case06/libresolarbox-v2_mobile/cadfiles/images/batterymount1c.png

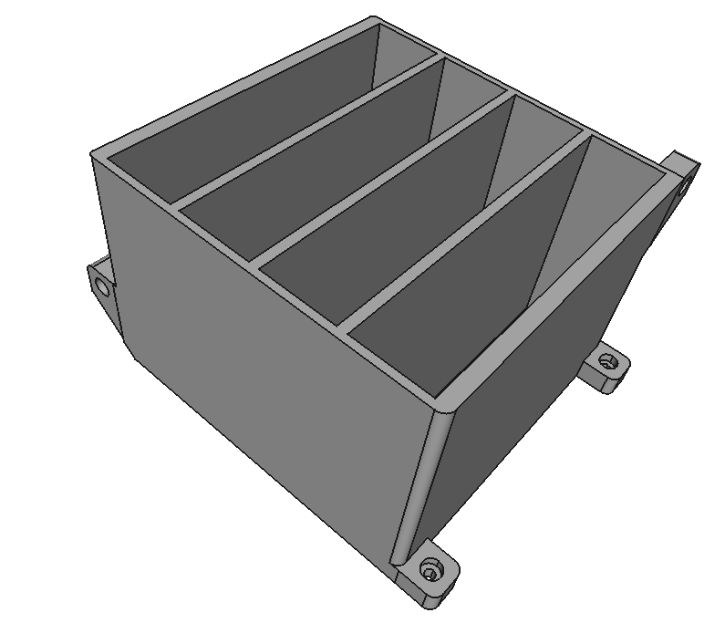
cadfiles/images/batterymount1c.png
