case06/libresolarbox-v2_mobile/cadfiles/images/batterymount_full-closure.PNG

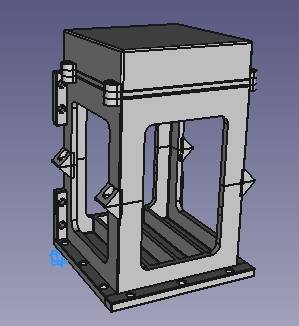
cadfiles/images/batterymount_full-closure.PNG
