case06/libresolarbox-v2_mobile/cadfiles/images/bms-case1h_box.png

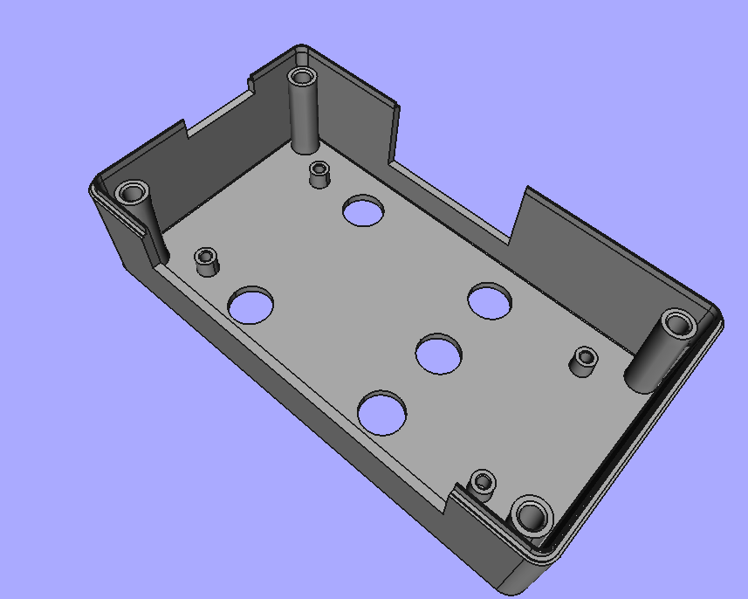
cadfiles/images/bms-case1h_box.png
