case06/libresolarbox-v2_mobile/cadfiles/images/bmscase1h_as.jpg

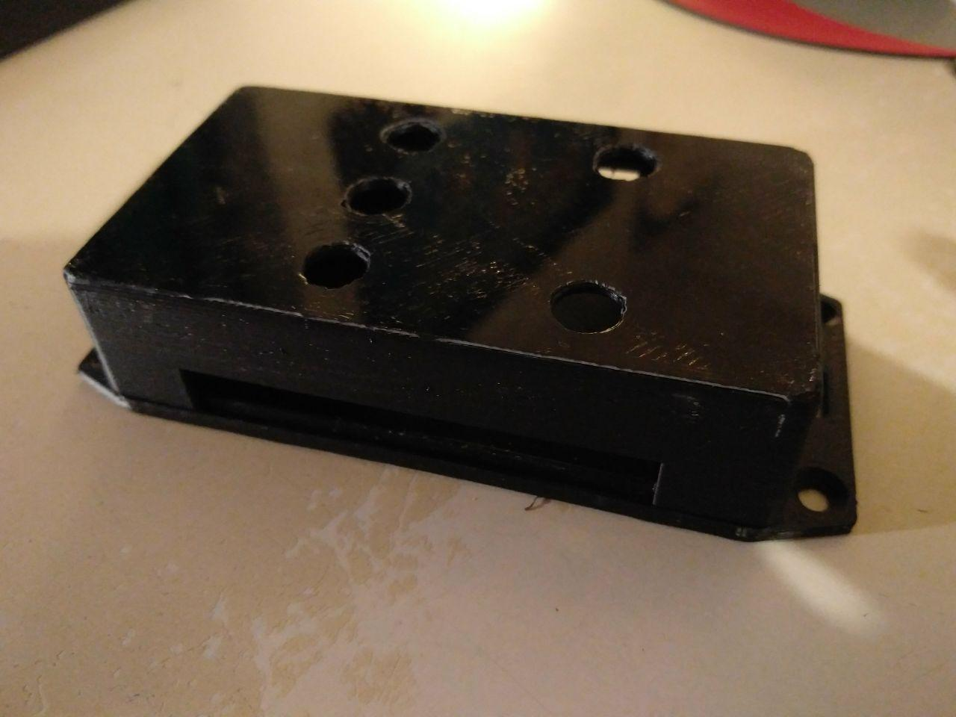
cadfiles/images/bmscase1h_as.jpg
