case06/libresolarbox-v2_mobile/cadfiles/images/bmscase1h_sp.jpg

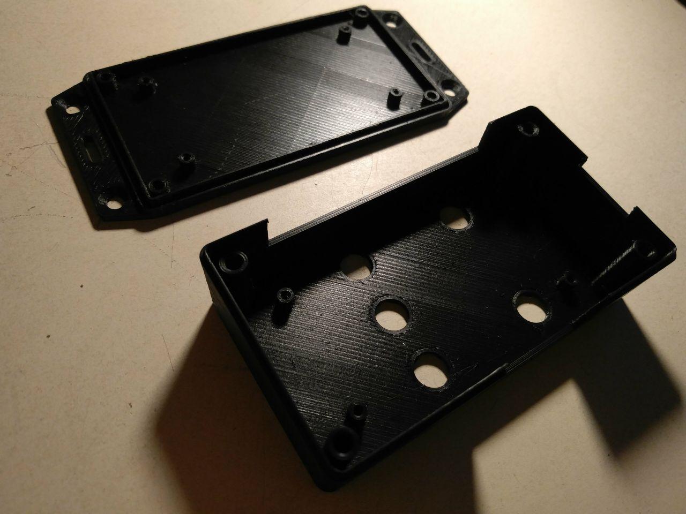
cadfiles/images/bmscase1h_sp.jpg
