case06/libresolarbox-v2_mobile/cadfiles/images/cam72_calb3.png

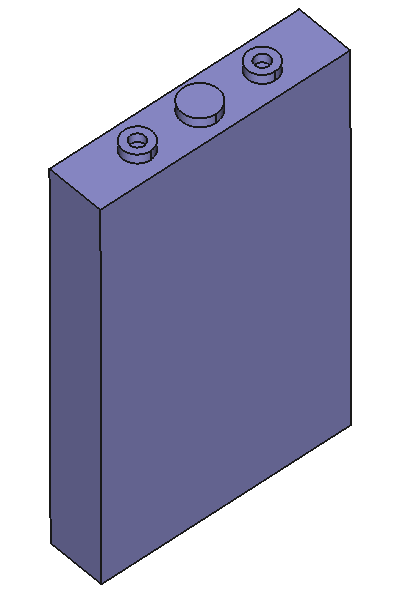
cadfiles/images/cam72_calb3.png
