case06/libresolarbox-v2_mobile/cadfiles/images/cam72_calb3_dimensions.png

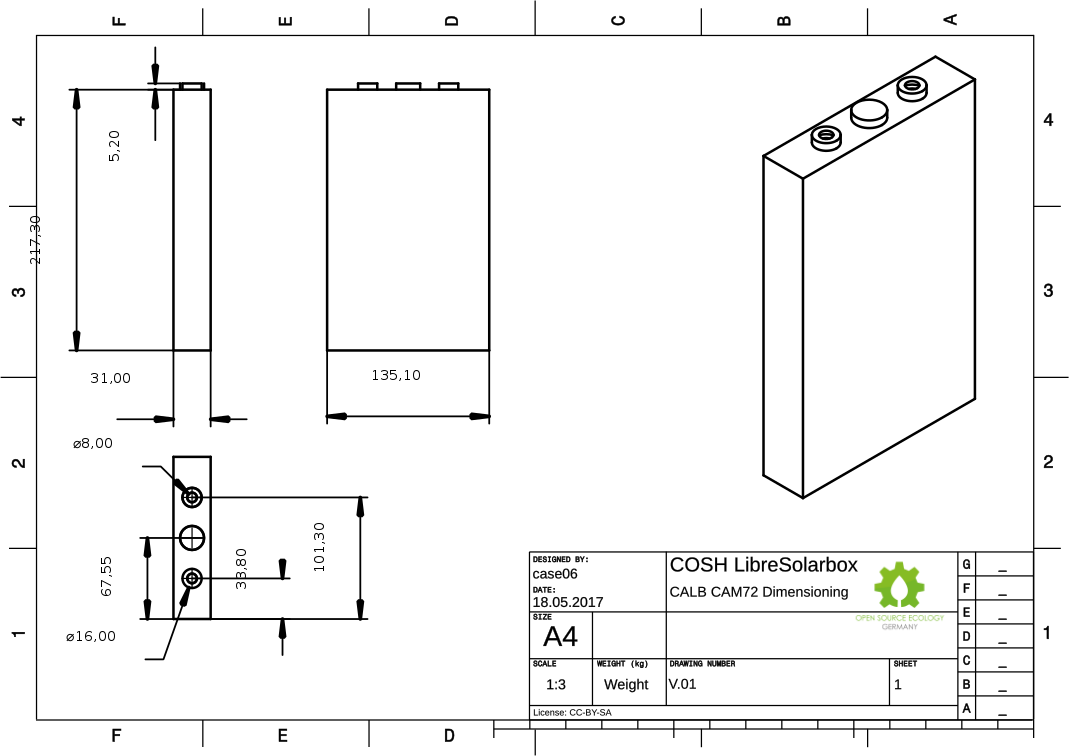
cadfiles/images/cam72_calb3_dimensions.png
