case06/libresolarbox-v2_mobile/cadfiles/images/front_dimensions.png

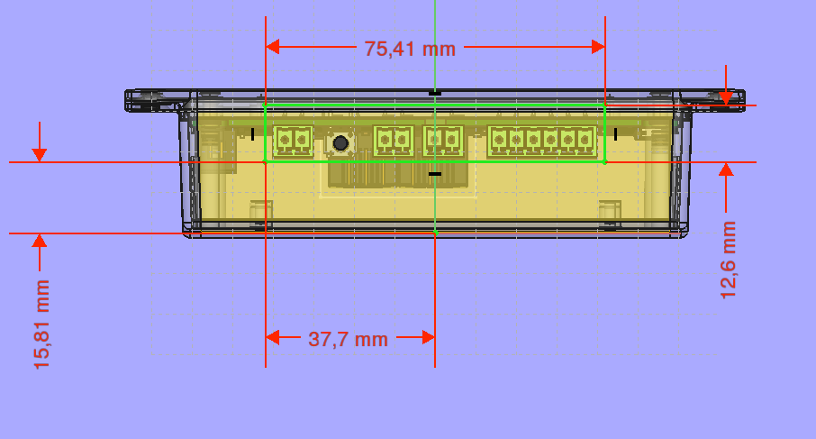
cadfiles/images/front_dimensions.png
