case06/libresolarbox-v2_mobile/cadfiles/images/Photo_2018-04-28_18-47-50.jpg

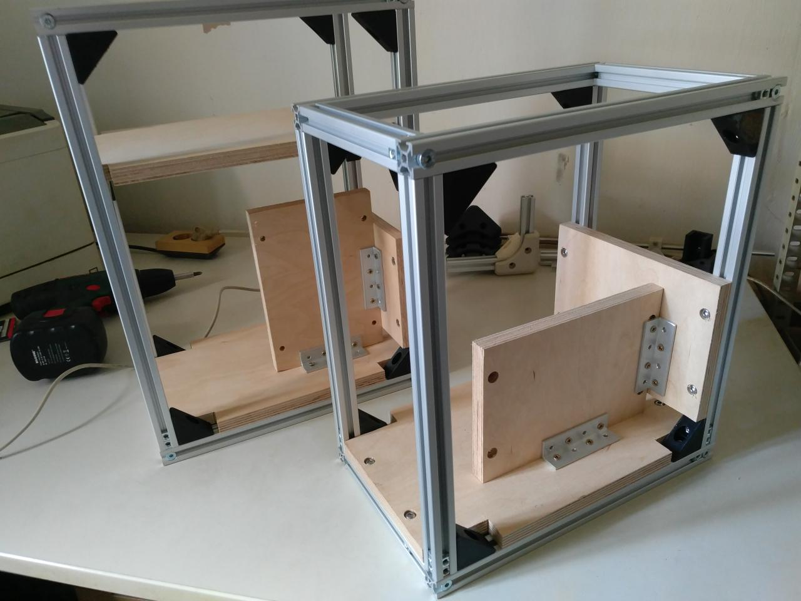
cadfiles/images/Photo_2018-04-28_18-47-50.jpg
