case06/libresolarbox-v2_mobile/cadfiles/images/Photo_2018-04-28_18-48-03.jpg

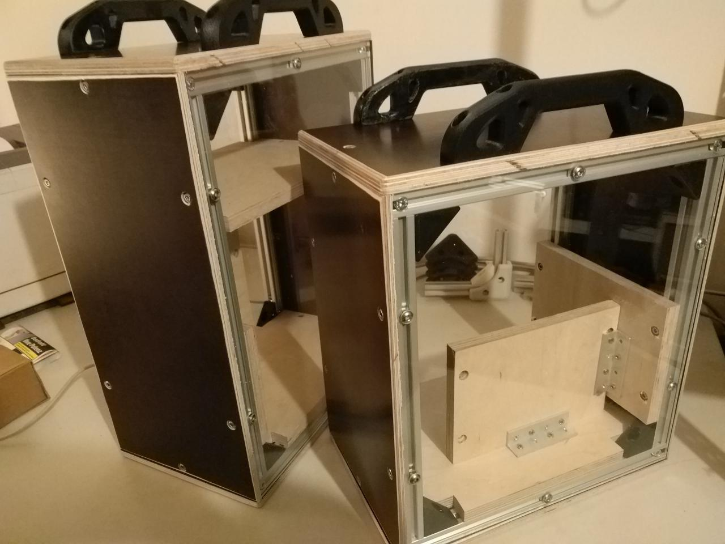
cadfiles/images/Photo_2018-04-28_18-48-03.jpg
