case06/libresolarbox-v2_mobile/cadfiles/images/sideCoverNG2.png

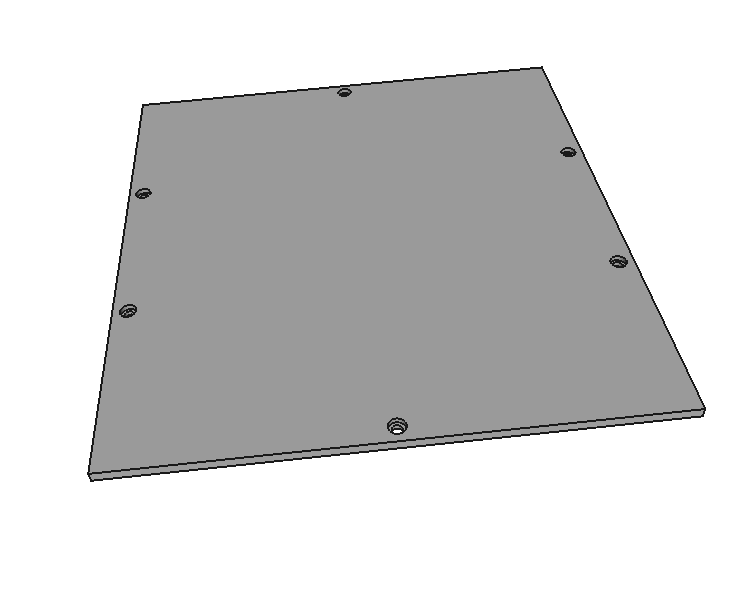
cadfiles/images/sideCoverNG2.png
