case06/libresolarbox-v2_mobile/cadfiles/images/sideCoverNG2_dim.png

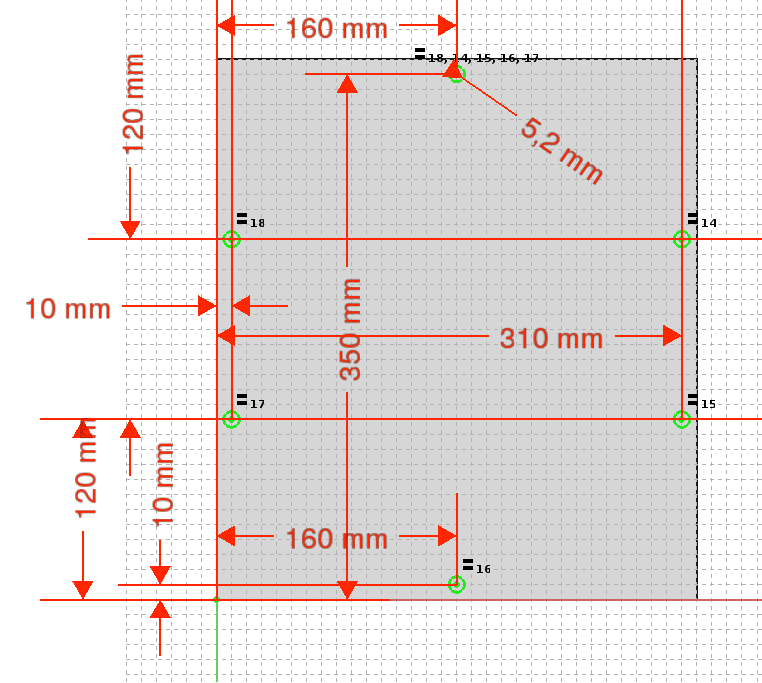
cadfiles/images/sideCoverNG2_dim.png
