case06/libresolarbox-v2_mobile/cadfiles/images/top_dimensions.png

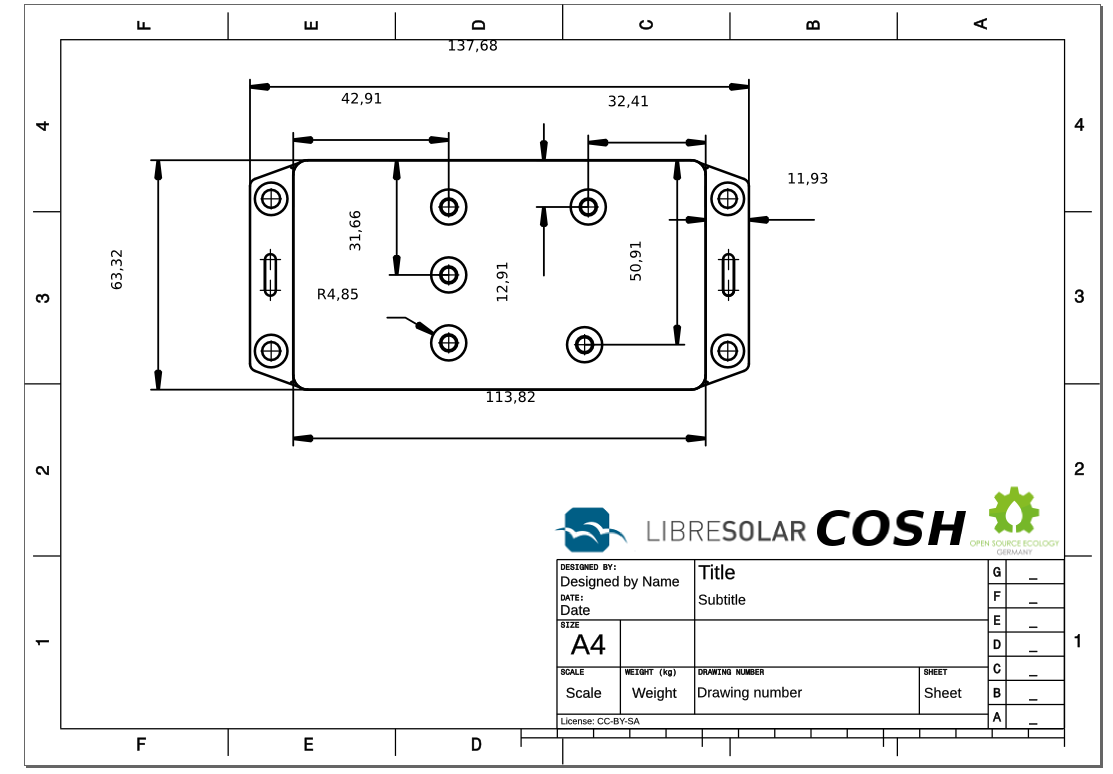
cadfiles/images/top_dimensions.png
