case06/libresolarbox-v2_mobile/cadfiles/images/topbottomNG2_dim.png

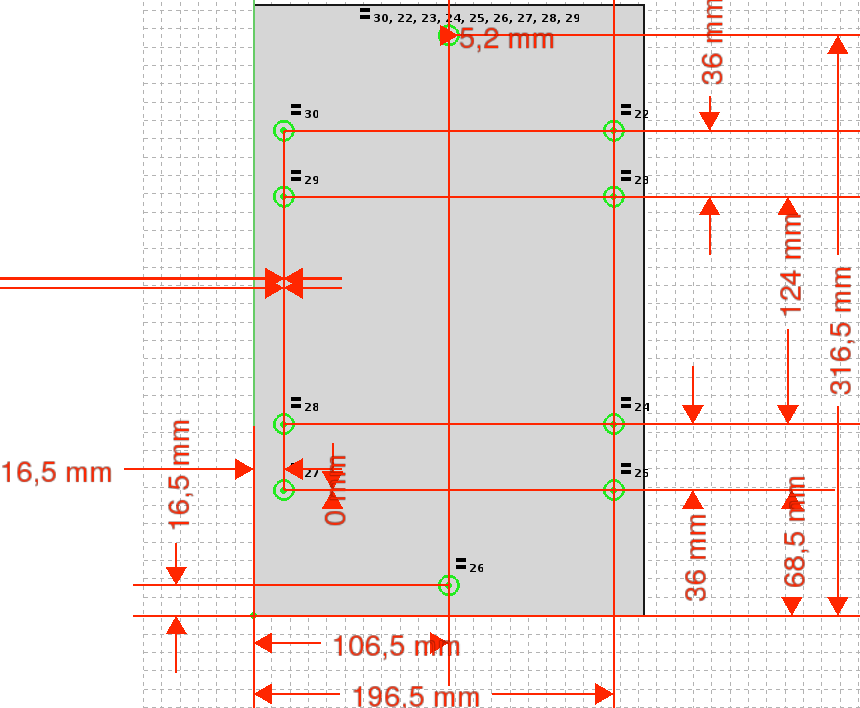
cadfiles/images/topbottomNG2_dim.png
