case06/libresolarbox-v2_mobile/cadfiles/images/topbottomNG2b.png

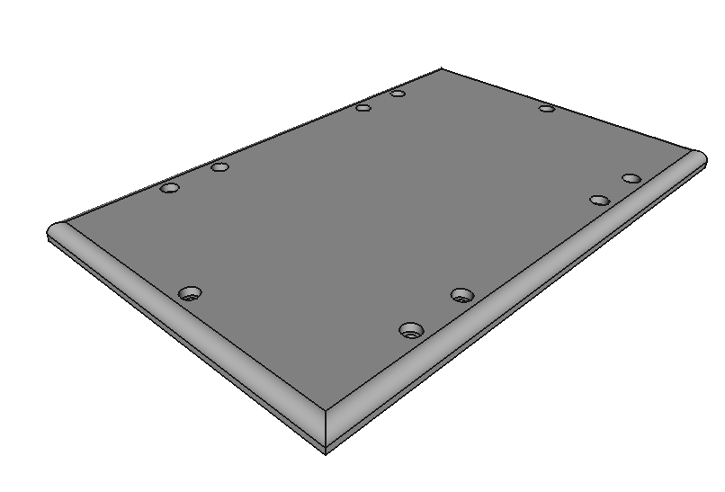
cadfiles/images/topbottomNG2b.png
