case06/libresolarbox-v2_mobile/cadfiles/images/UPKframeNG2b.png

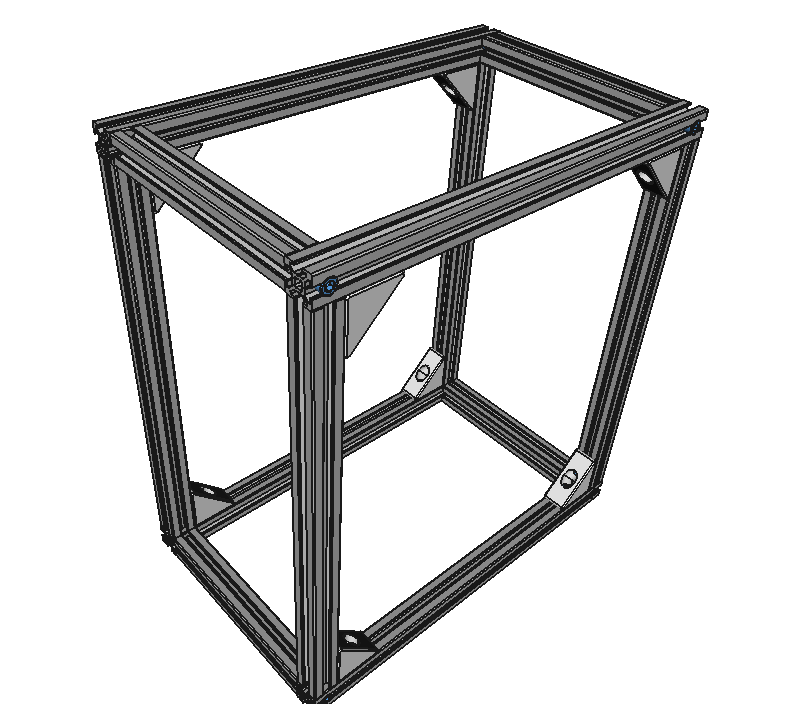
cadfiles/images/UPKframeNG2b.png
