case06/libresolarbox-v2_mobile/cadfiles/images/UPKframeNG2d.png

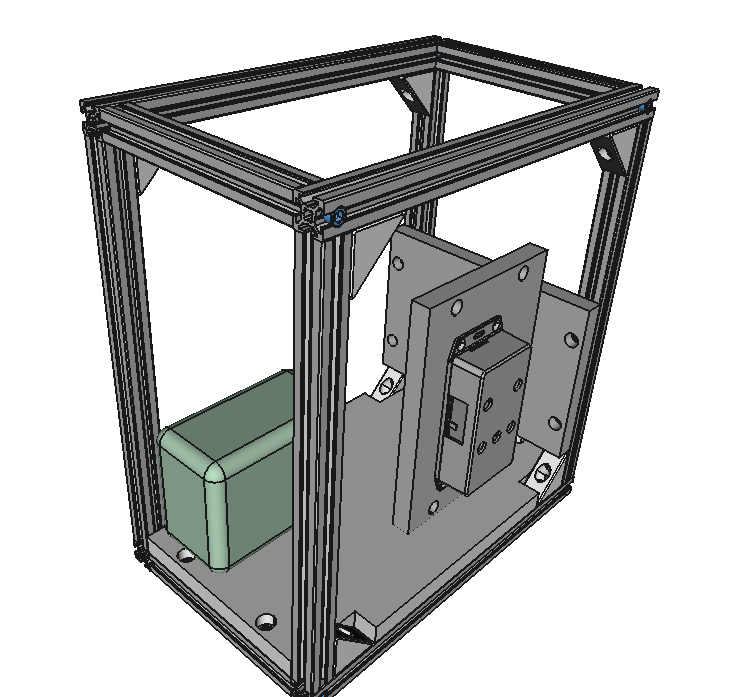
cadfiles/images/UPKframeNG2d.png
