case06/libresolarbox-v2_mobile/cadfiles/images/UPKframeNG2e.png

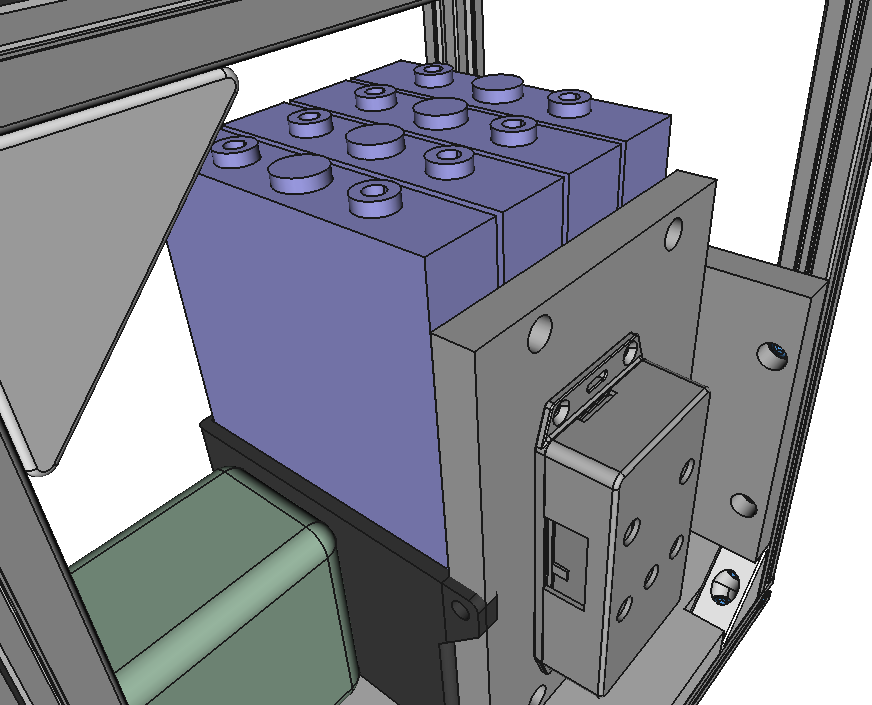
cadfiles/images/UPKframeNG2e.png
