case06/libresolarbox-v2_mobile/cadfiles/images/UPKframeNG2e_closeup.png

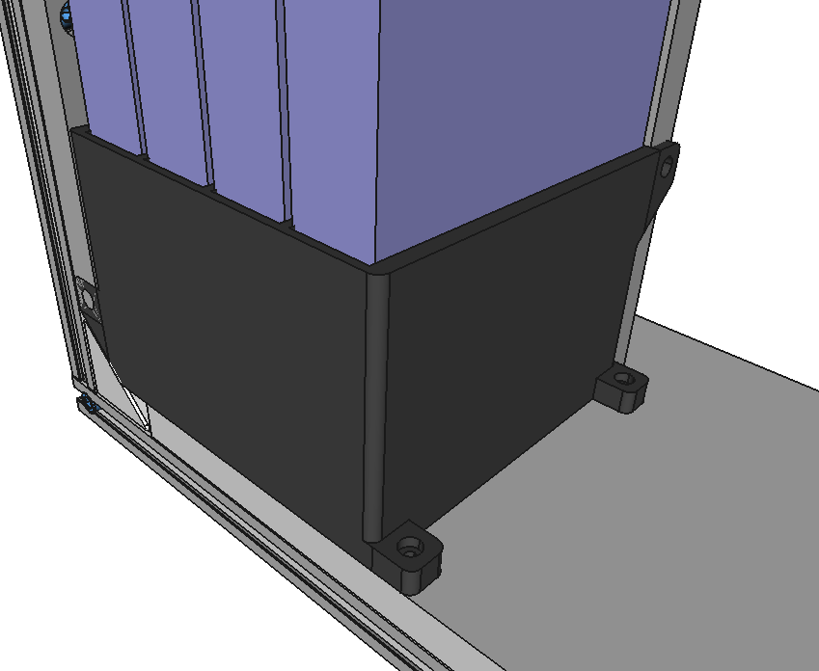
cadfiles/images/UPKframeNG2e_closeup.png
