case06/libresolarbox-v2_mobile/cadfiles/images/UPKframeNG2h_closeup.png

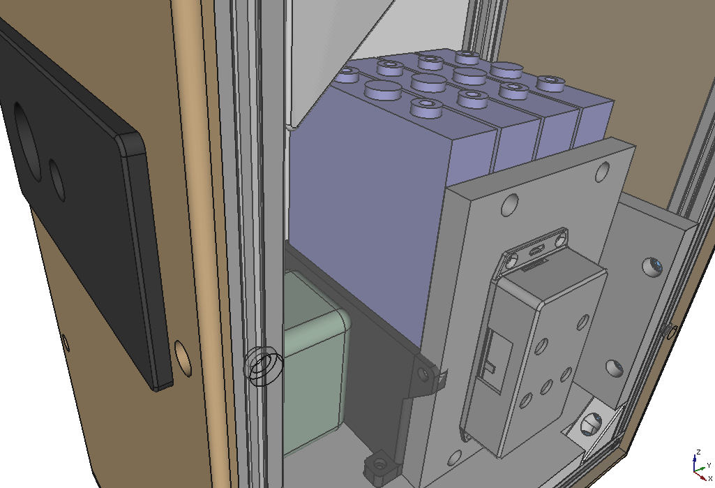
cadfiles/images/UPKframeNG2h_closeup.png
