case06/libresolarbox-v2_mobile/cadfiles/images/UPKframeNG2j.png

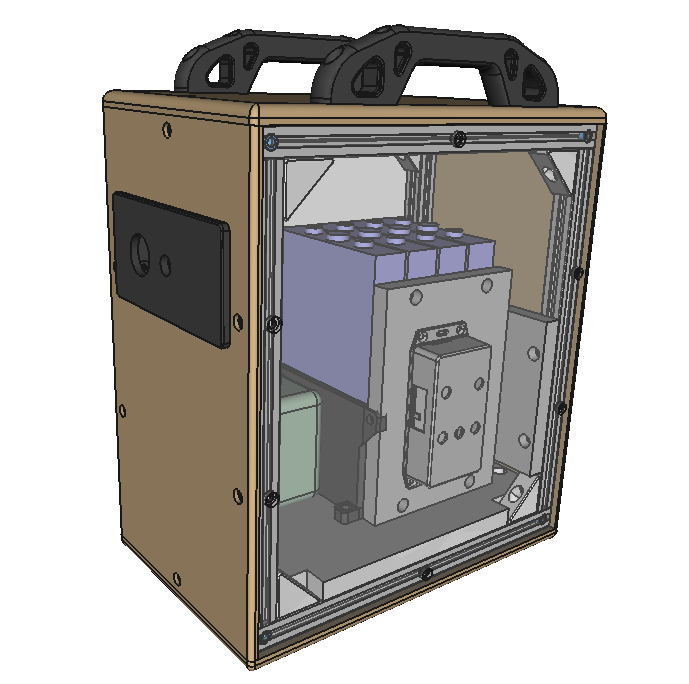
cadfiles/images/UPKframeNG2j.png
