case06/libresolarbox-v2_mobile/cadfiles/images/UPKframeNG2j_back.png

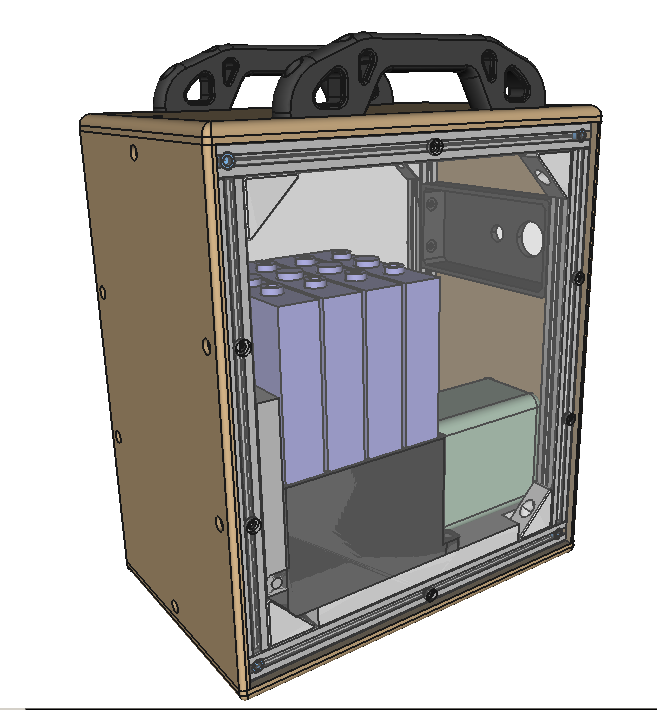
cadfiles/images/UPKframeNG2j_back.png
