case06/libresolarbox-v2_mobile/electronics/images/P7080123.JPG

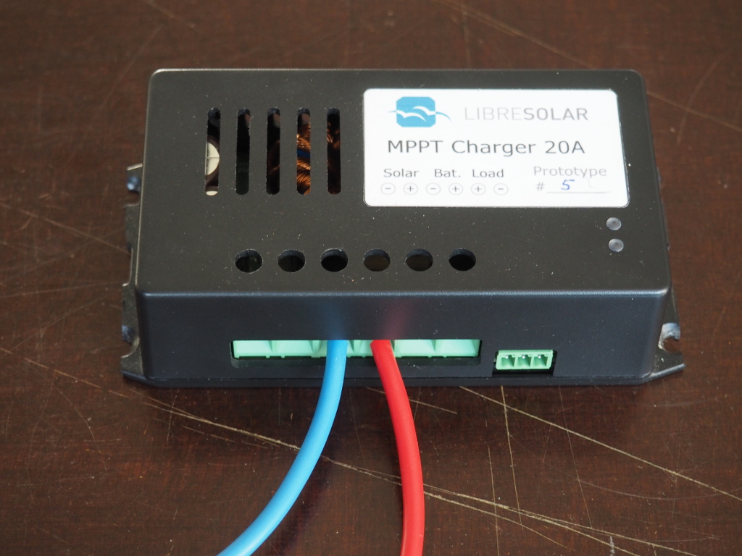
electronics/images/P7080123.JPG
