case06/libresolarbox-v2_mobile/cadfiles/cam72_calb3.fcstd

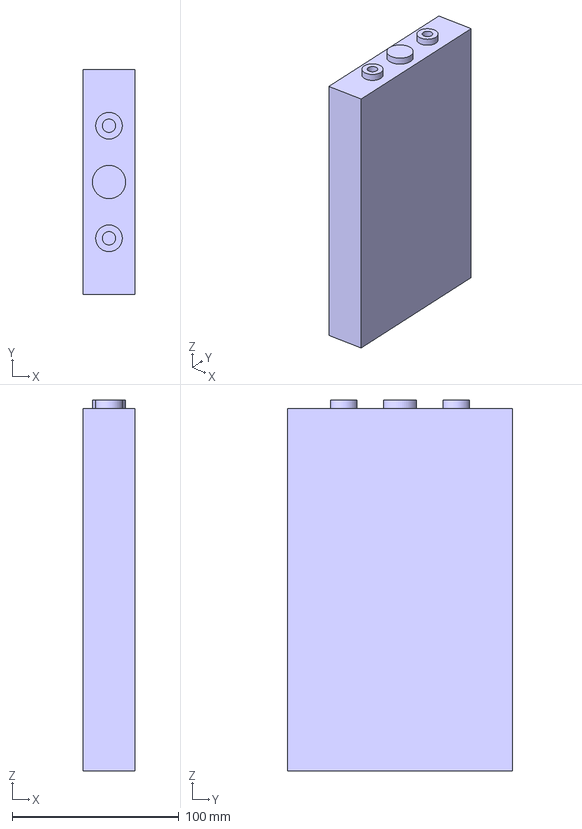
[picture p52: CAD file, 2021-08-01]
cadfiles/cam72_calb3.fcstd
31.0 x 135.1 x 222.5 mm
