case06/libresolarbox-v2_mobile/doc/src/src_boxassemblyguide1d/upright/upright5_all.fcstd

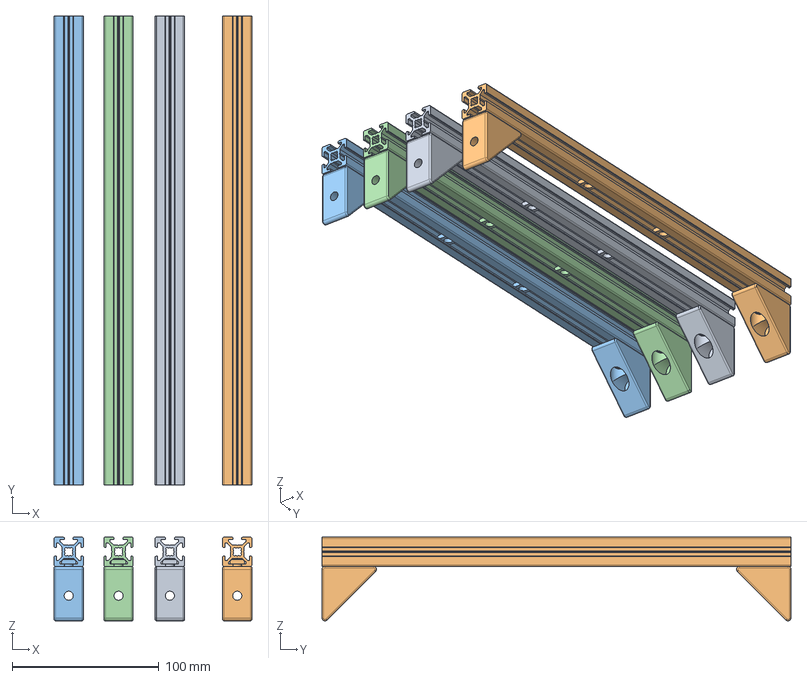
[picture p55: CAD file, 2021-08-01]
doc/src/src_boxassemblyguide1d/upright/upright5_all.fcstd
135.0 x 320.0 x 57.2 mm
