case06/libresolarbox-v2_mobile/doc/src/src_boxassemblyguide1d/upright/upright3_ex.fcstd

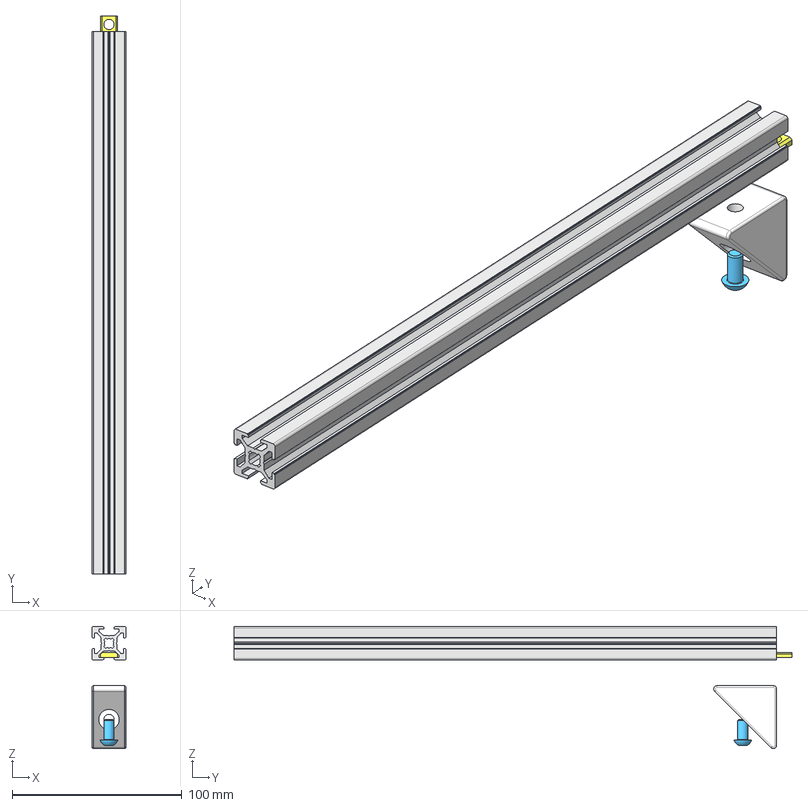
[picture p58: CAD file, 2021-08-01]
doc/src/src_boxassemblyguide1d/upright/upright3_ex.fcstd
20.0 x 329.0 x 72.2 mm
tslot32
m6nutplate
M6x12-Screw001
RAcorner
