case06/libresolarbox-v2_mobile/doc/src/src_boxassemblyguide1d/rawframe/rawframe2.fcstd

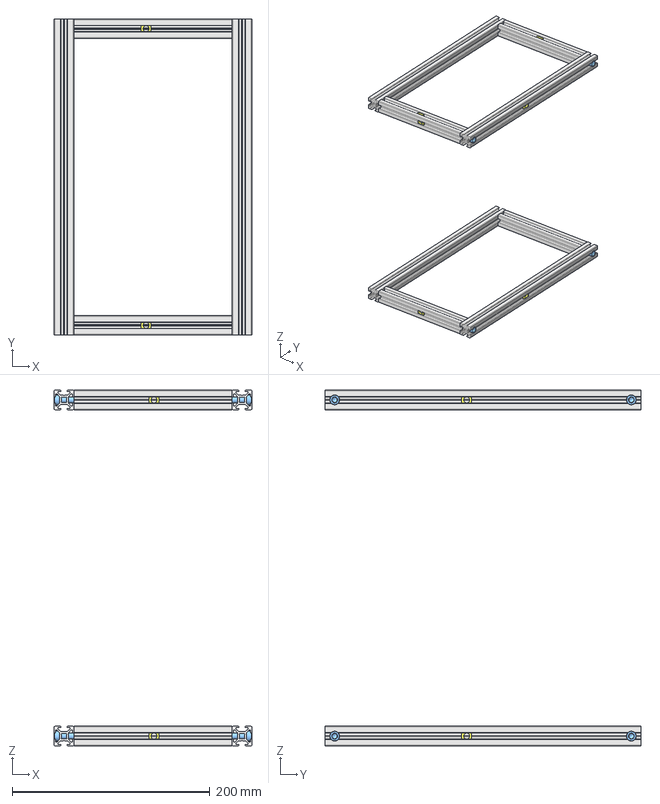
[picture p59: CAD file, 2021-08-01]
doc/src/src_boxassemblyguide1d/rawframe/rawframe2.fcstd
200.0 x 320.0 x 360.0 mm
tslot32con
tslot16
tslot16_001
tslot32con_001
M6x25-Screw
M6x25-Screw004
M6x25-Screw005
M6x25-Screw006
tslot32con001
tslot041
tslot16_002
tslot32con_002
M6x25-Screw012
M6x25-Screw015
M6x25-Screw017
M6x25-Screw016
m6nutplate020uf
m6nutplate021lf
m6nutplate022lf
m6nutplate023lf
m6nutplate024lf
m6nutplate025lf
m6nutplate026lf
m6nutplate027lf
m6nutplate028uf
m6nutplate029uf
m6nutplate030lf
m6nutplate031lf
m6nutplate032uf
m6nutplate033lf
m6nutplate025uf001
m6nutplate022uf001
