case06/libresolarbox-v2_mobile/doc/src/src_boxassemblyguide1d/upright/upright3.fcstd

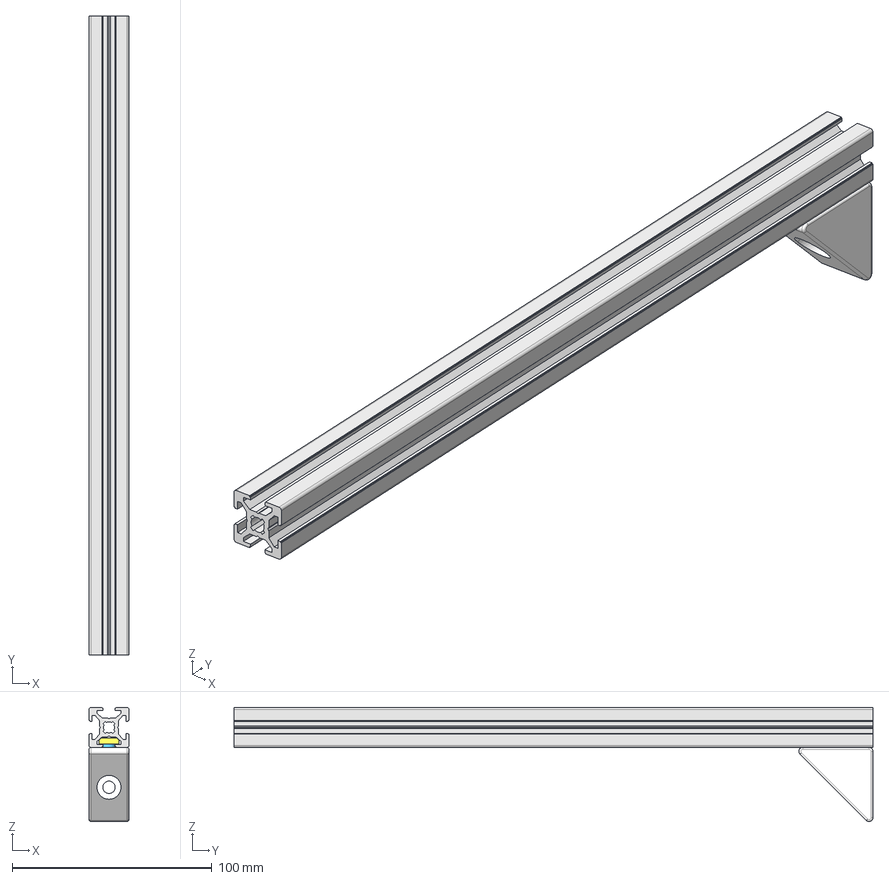
[picture p60: CAD file, 2021-08-01]
doc/src/src_boxassemblyguide1d/upright/upright3.fcstd
20.0 x 320.0 x 57.2 mm
tslot32
m6nutplate
M6x12-Screw001
RAcorner
