case06/libresolarbox-v2_mobile/doc/src/src_boxassemblyguide1d/upright/upright1.fcstd

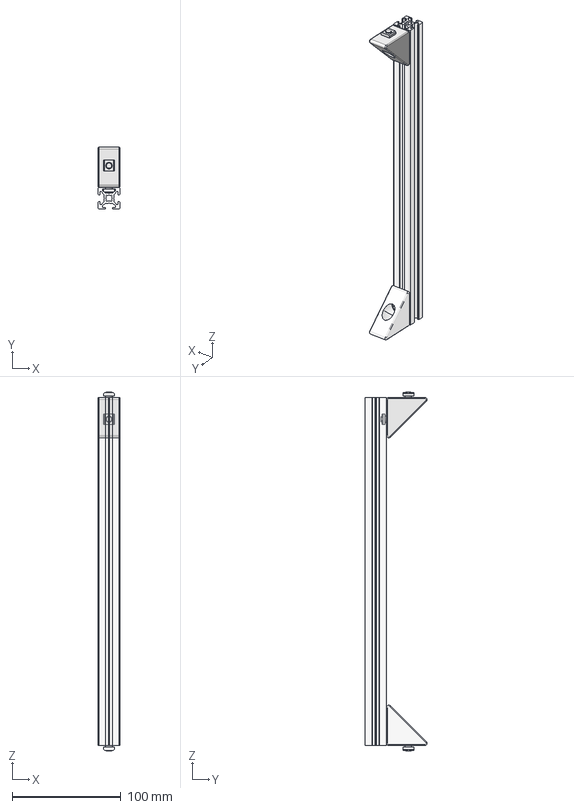
[picture p61: CAD file, 2021-08-01]
doc/src/src_boxassemblyguide1d/upright/upright1.fcstd
20.0 x 57.2 x 330.0 mm
tslot32_001
