case06/libresolarbox-v2_mobile/doc/src/images/assembly_day_08.07.18/P7080107.JPG

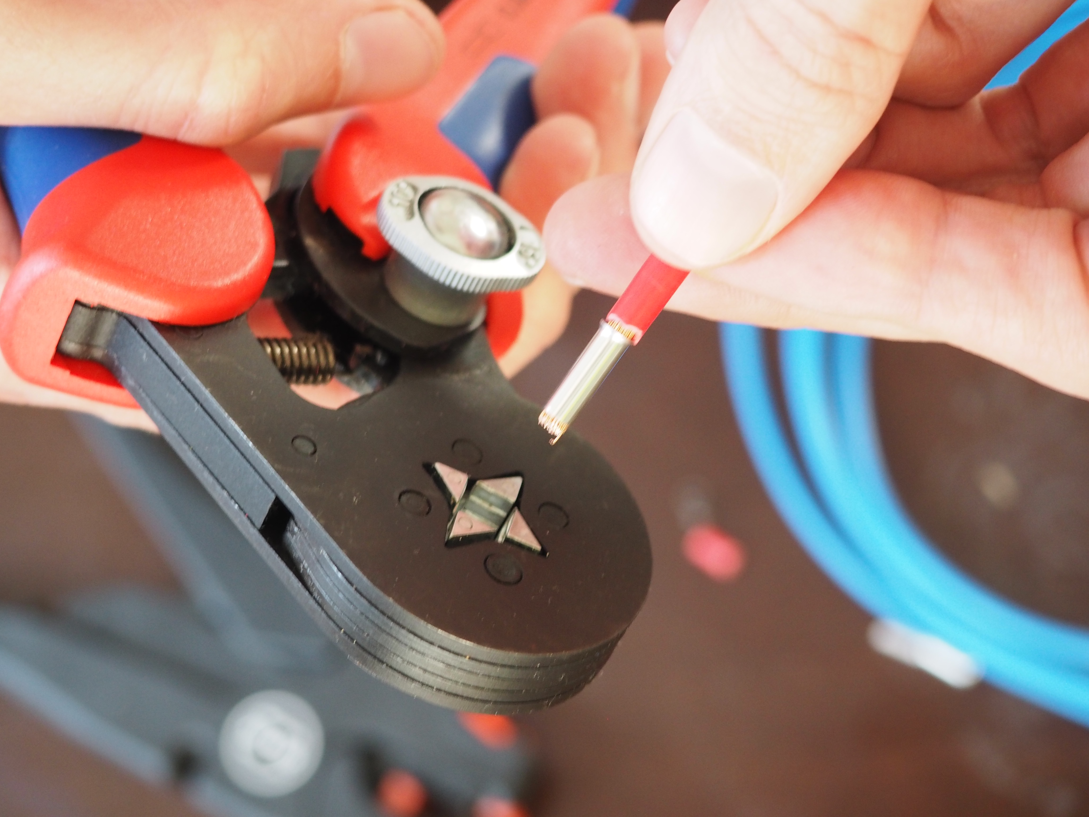
doc/src/images/assembly_day_08.07.18/P7080107.JPG
