case06/libresolarbox-v2_mobile/doc/src/src_boxassemblyguide1d/box-assemblyguide/images/titlepage.png

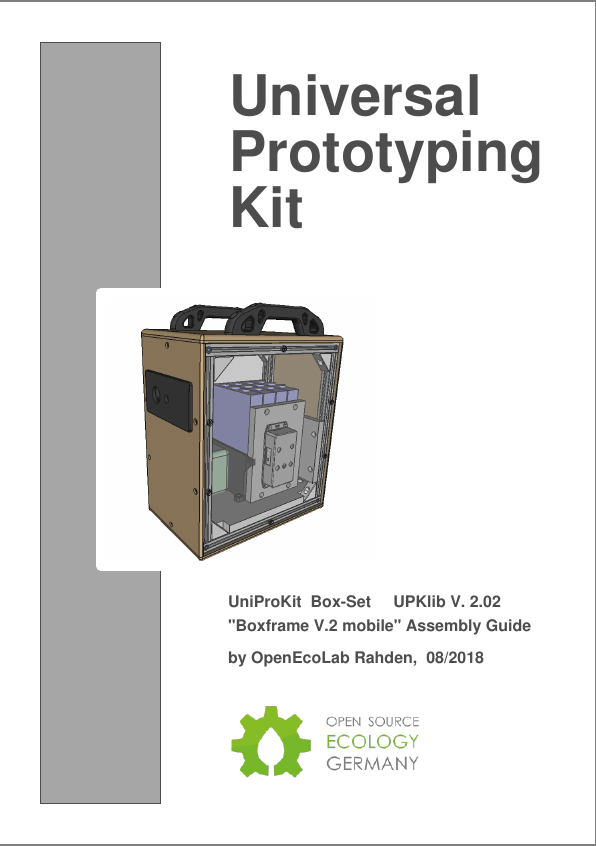
doc/src/src_boxassemblyguide1d/box-assemblyguide/images/titlepage.png
