case06/libresolarbox-v2_mobile/doc/src/src_boxassemblyguide1d/cover/cov10.png

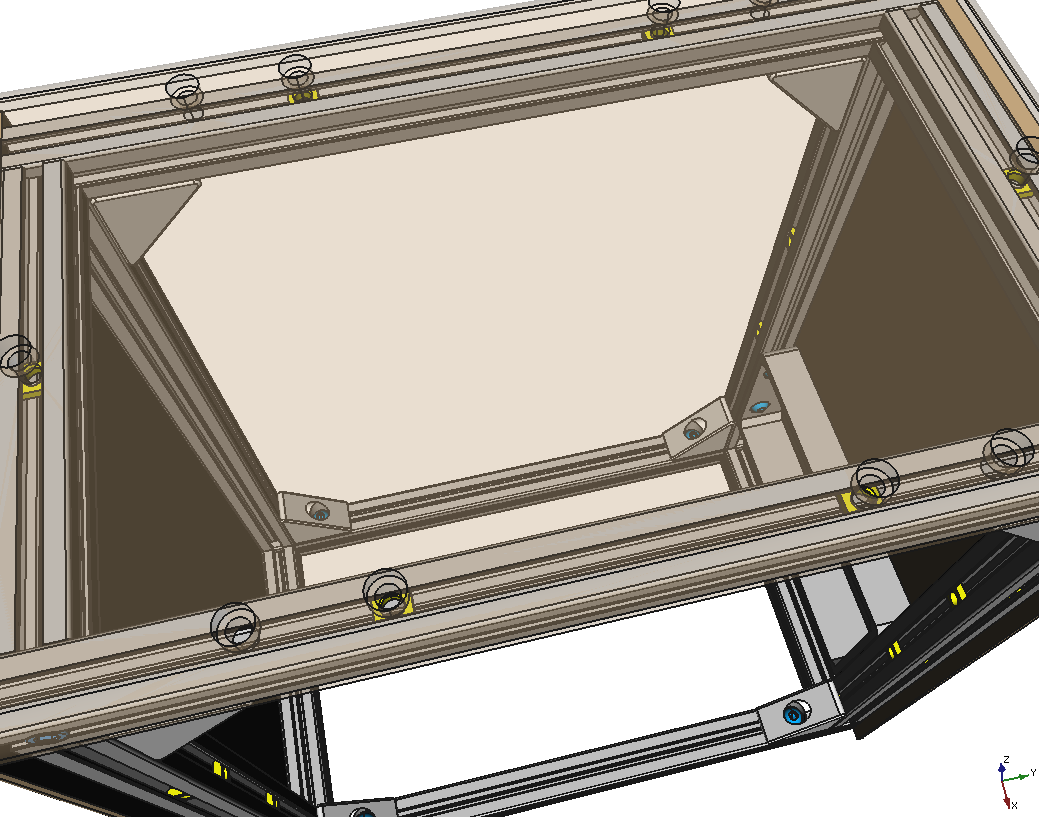
doc/src/src_boxassemblyguide1d/cover/cov10.png
