case06/libresolarbox-v2_mobile/doc/src/src_boxassemblyguide1d/cover/cov16.png

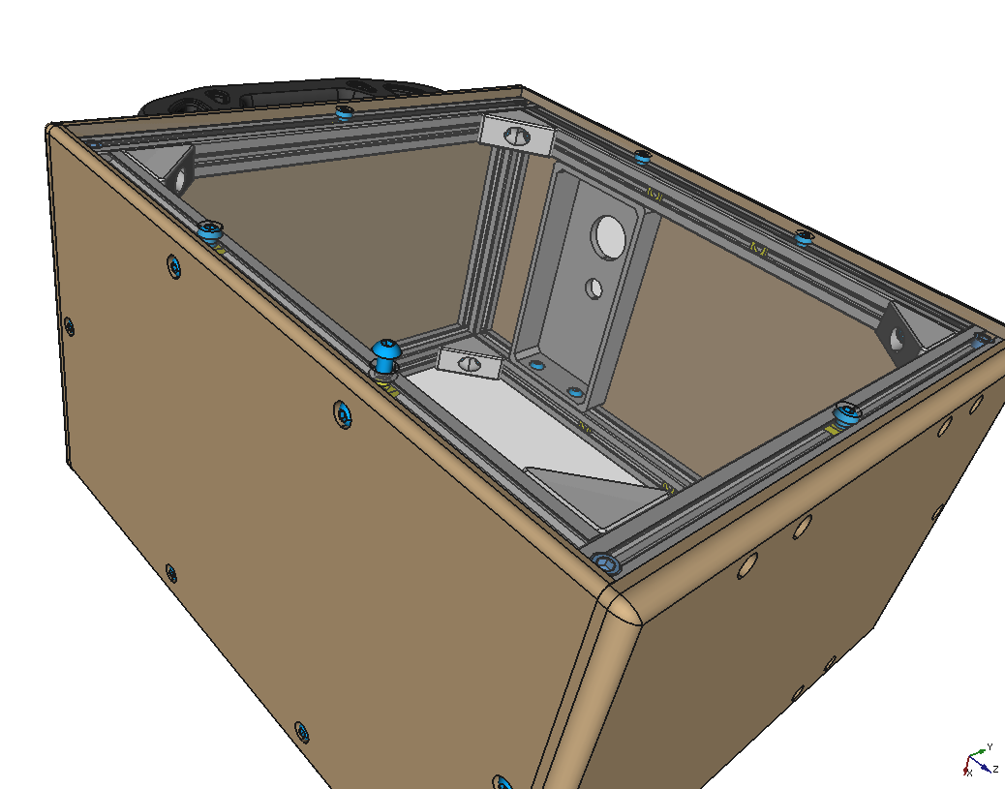
doc/src/src_boxassemblyguide1d/cover/cov16.png
