case06/libresolarbox-v2_mobile/doc/src/src_boxassemblyguide1d/ifmountframe/ifmount1.png

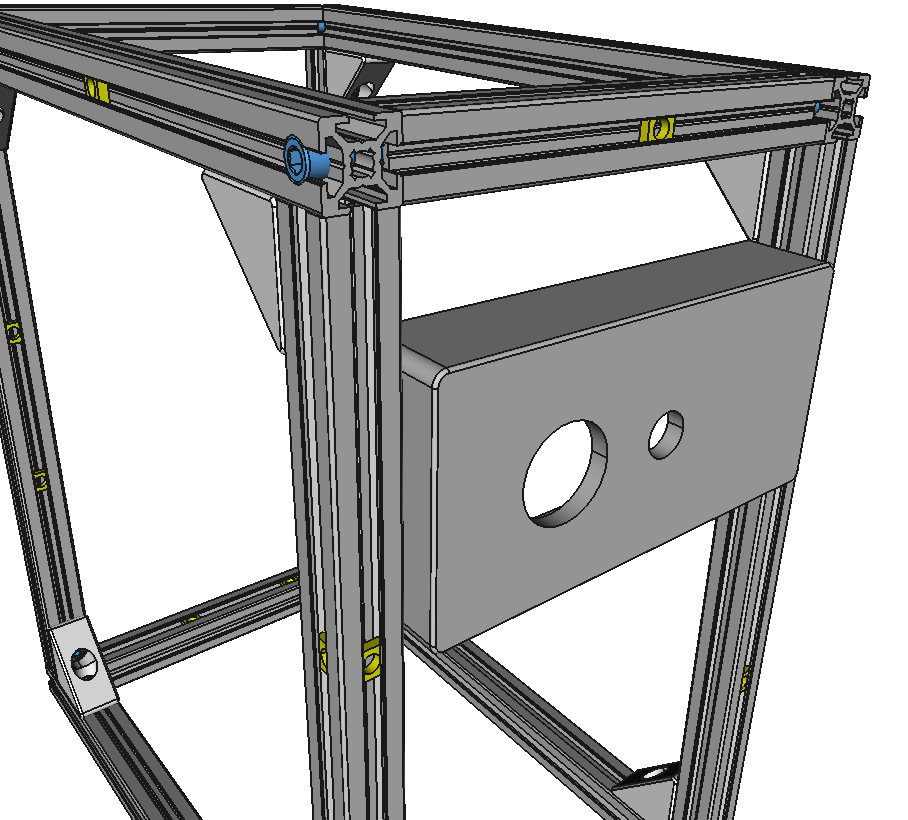
doc/src/src_boxassemblyguide1d/ifmountframe/ifmount1.png
