case06/libresolarbox-v2_mobile/doc/src/src_boxassemblyguide1d/innerplates/bottom1b.png

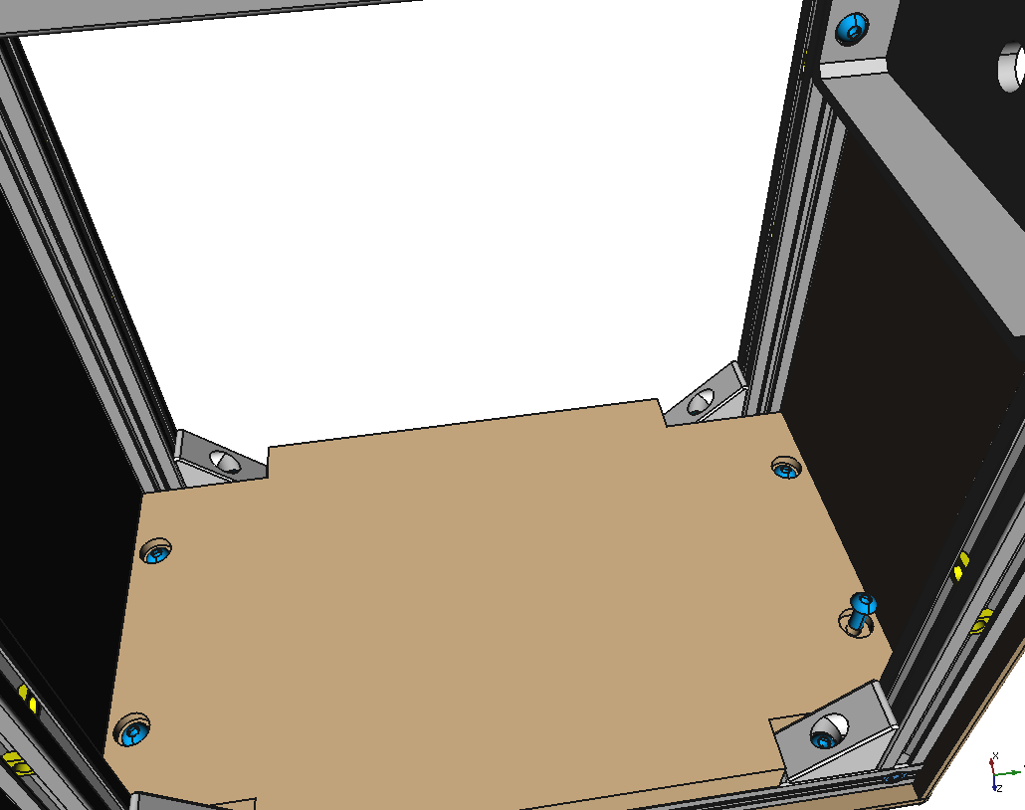
doc/src/src_boxassemblyguide1d/innerplates/bottom1b.png
