case06/libresolarbox-v2_mobile/doc/src/src_boxassemblyguide1d/innerplates/front4c.png

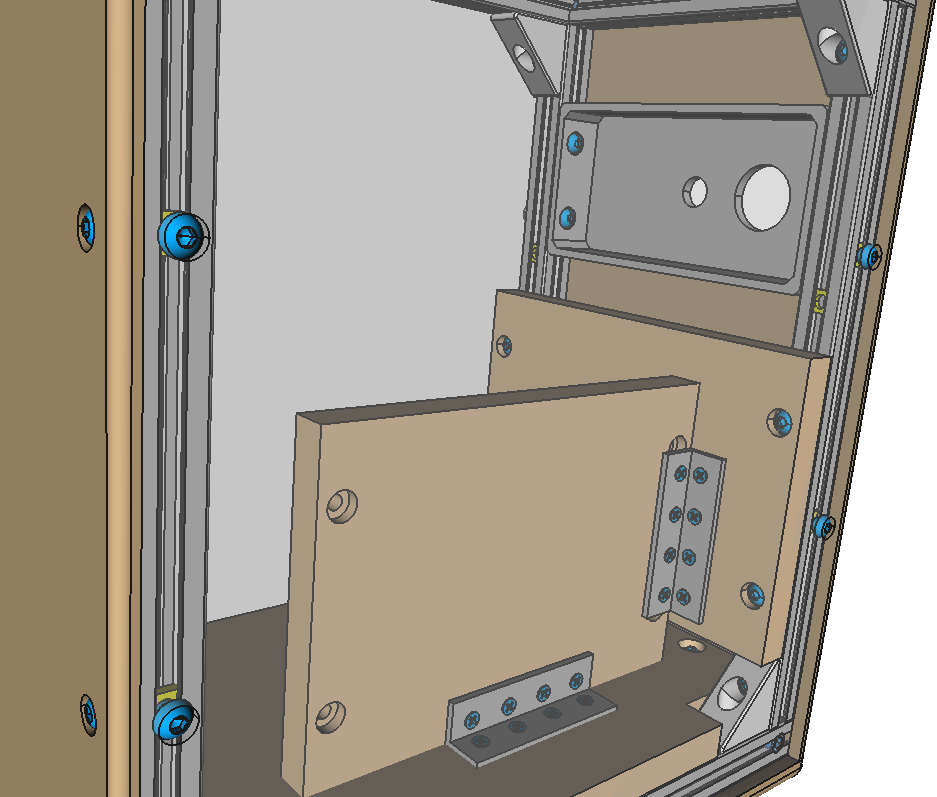
doc/src/src_boxassemblyguide1d/innerplates/front4c.png
