case06/libresolarbox-v2_mobile/doc/src/src_boxassemblyguide1d/lower_frame/lframe2.png

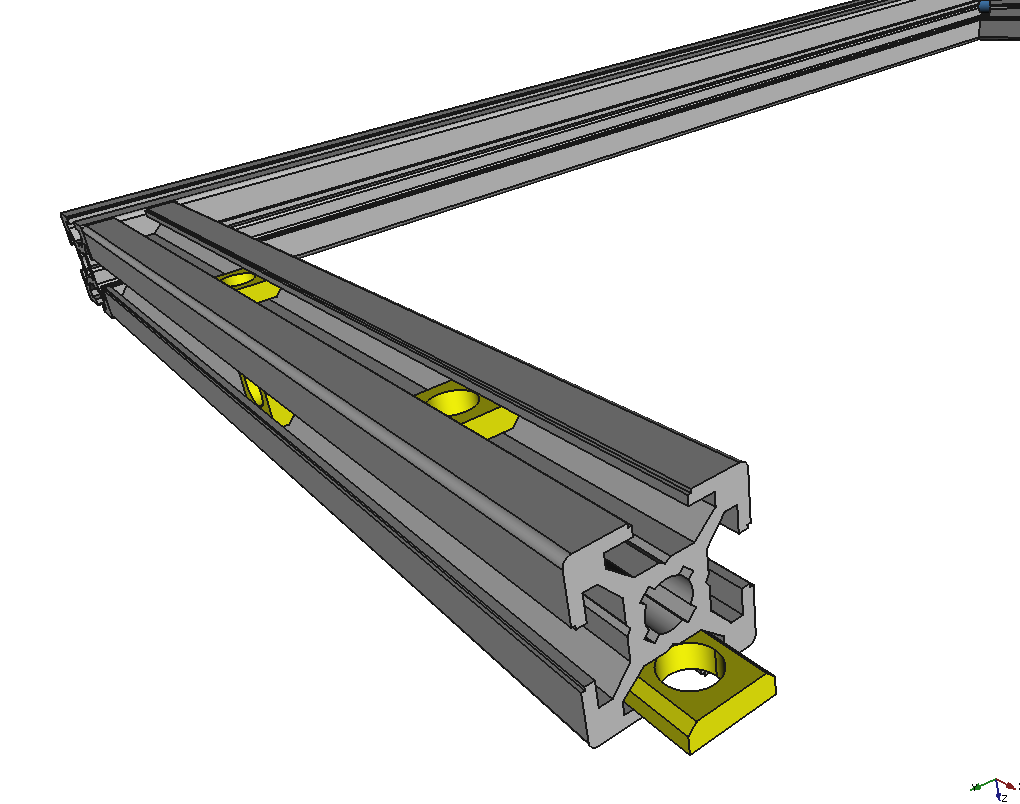
doc/src/src_boxassemblyguide1d/lower_frame/lframe2.png
