case06/libresolarbox-v2_mobile/doc/src/src_boxassemblyguide1d/lower_frame/lframe3.png

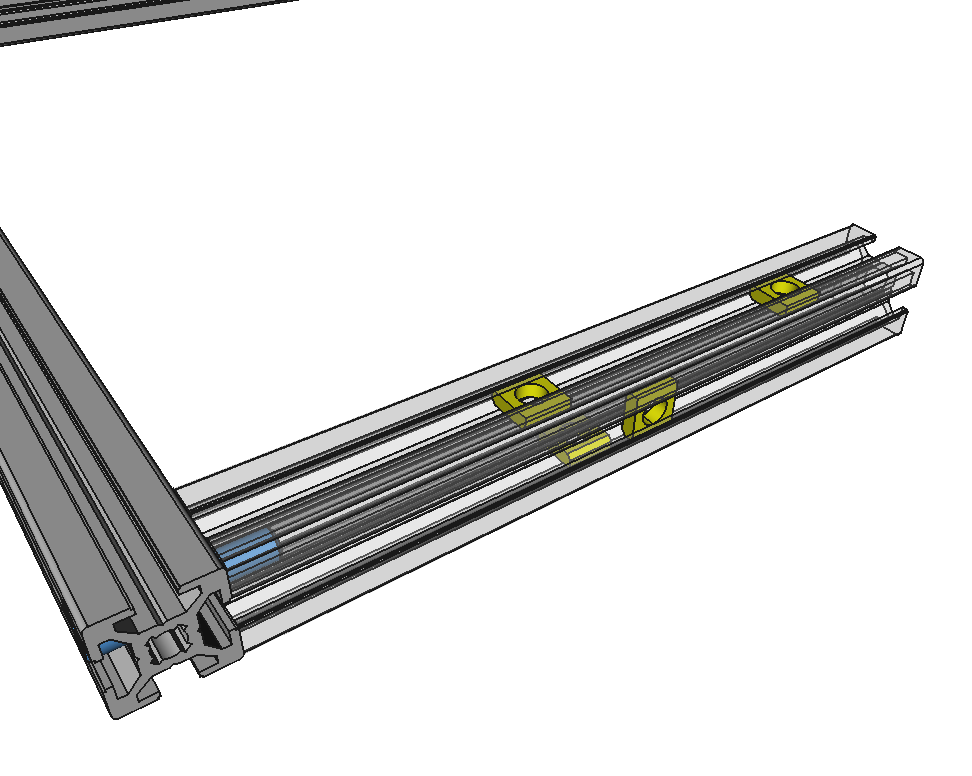
doc/src/src_boxassemblyguide1d/lower_frame/lframe3.png
