case06/libresolarbox-v2_mobile/doc/src/src_boxassemblyguide1d/rawframe/junction2.png

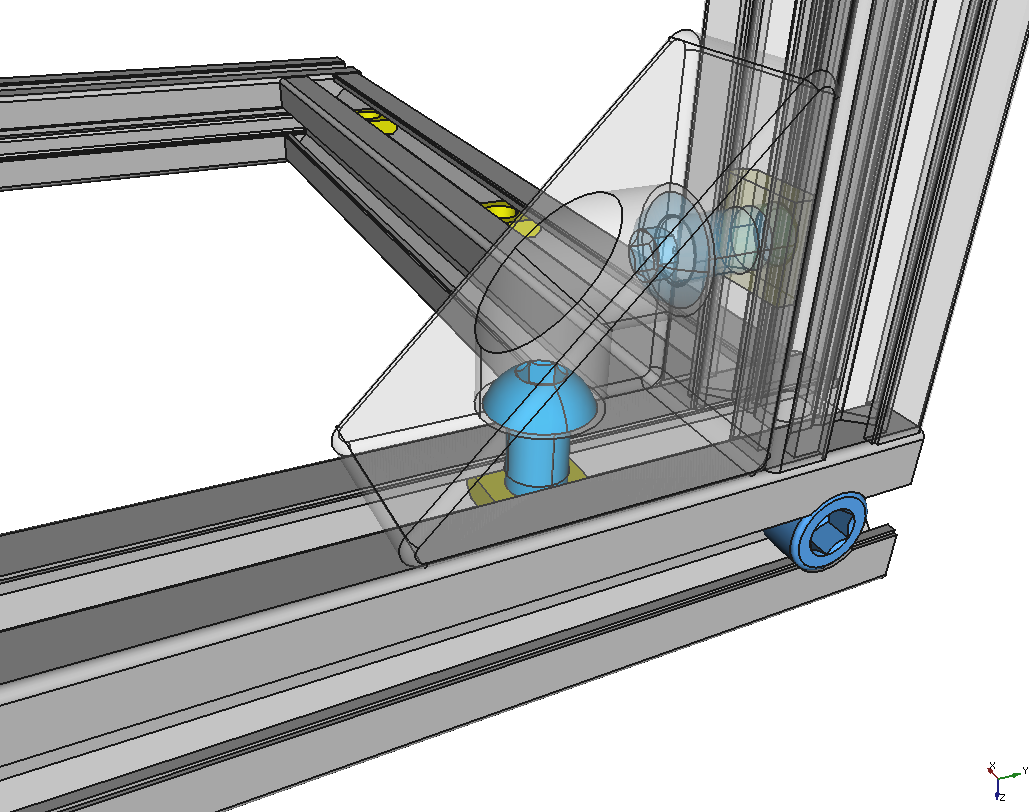
doc/src/src_boxassemblyguide1d/rawframe/junction2.png
