case06/libresolarbox-v2_mobile/doc/src/src_boxassemblyguide1d/rawframe/junction15.png

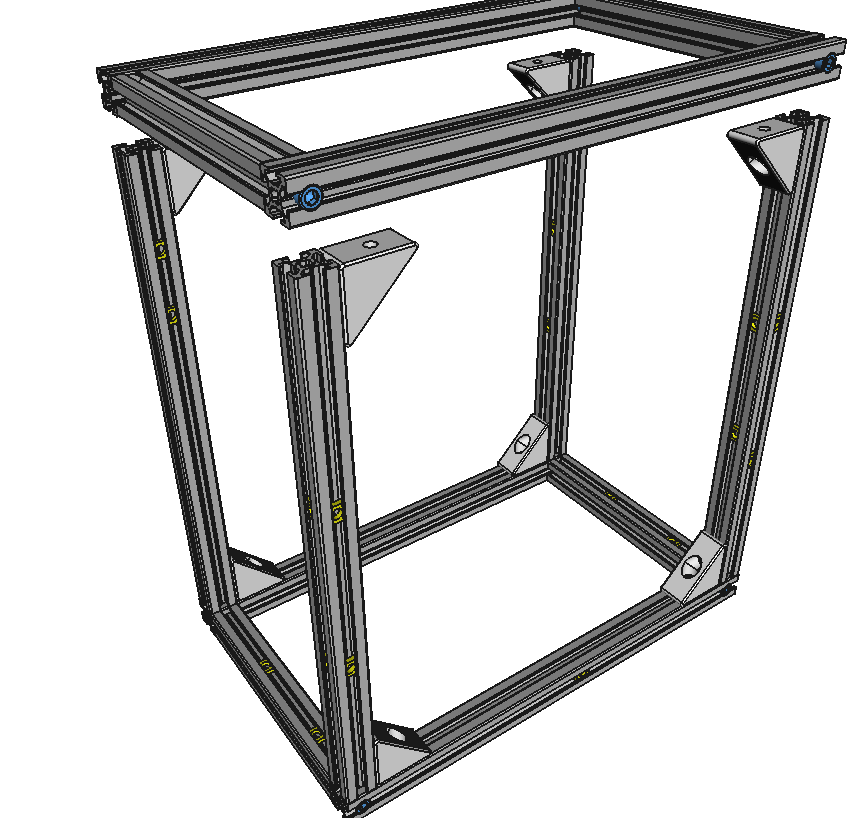
doc/src/src_boxassemblyguide1d/rawframe/junction15.png
