case06/libresolarbox-v2_mobile/doc/src/src_boxassemblyguide1d/rawframe/junction17b.png

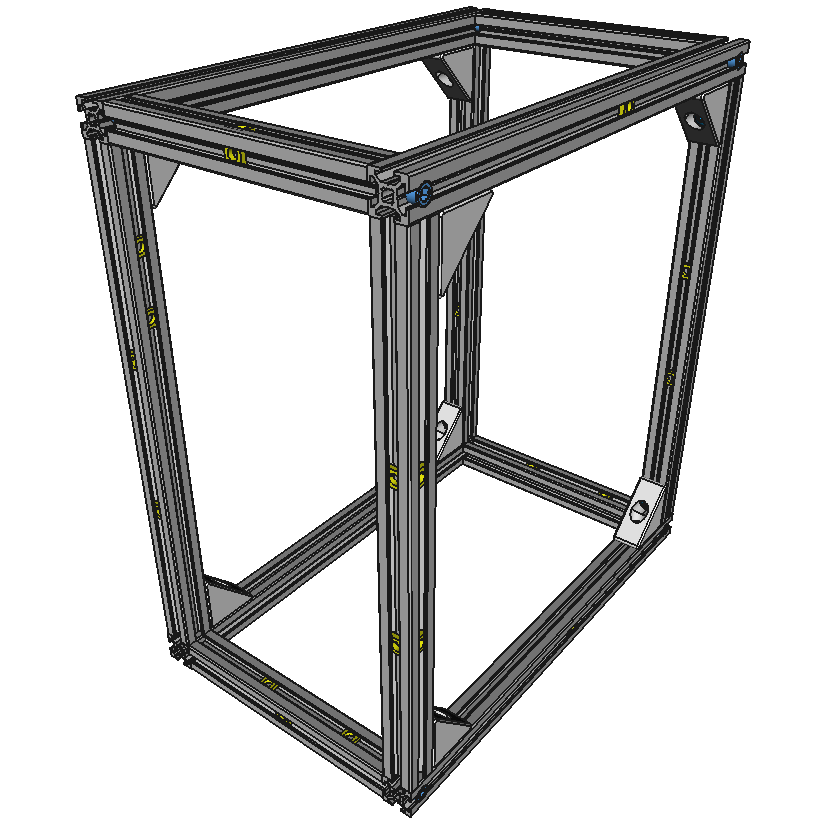
doc/src/src_boxassemblyguide1d/rawframe/junction17b.png
