case06/libresolarbox-v2_mobile/doc/src/src_boxassemblyguide1d/upper_frame/corner_junction1.png

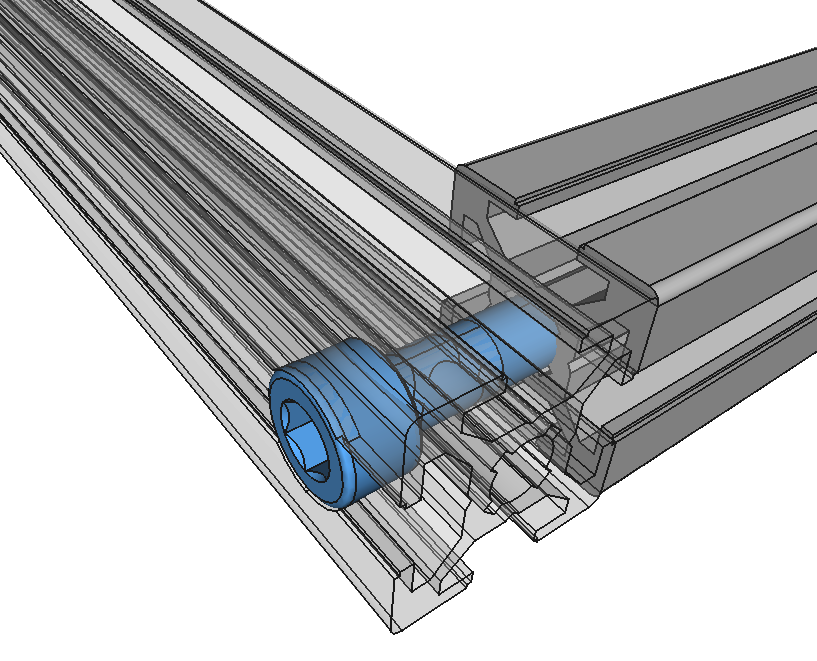
doc/src/src_boxassemblyguide1d/upper_frame/corner_junction1.png
