case06/libresolarbox-v2_mobile/doc/src/src_boxassemblyguide1d/upper_frame/frame5.png

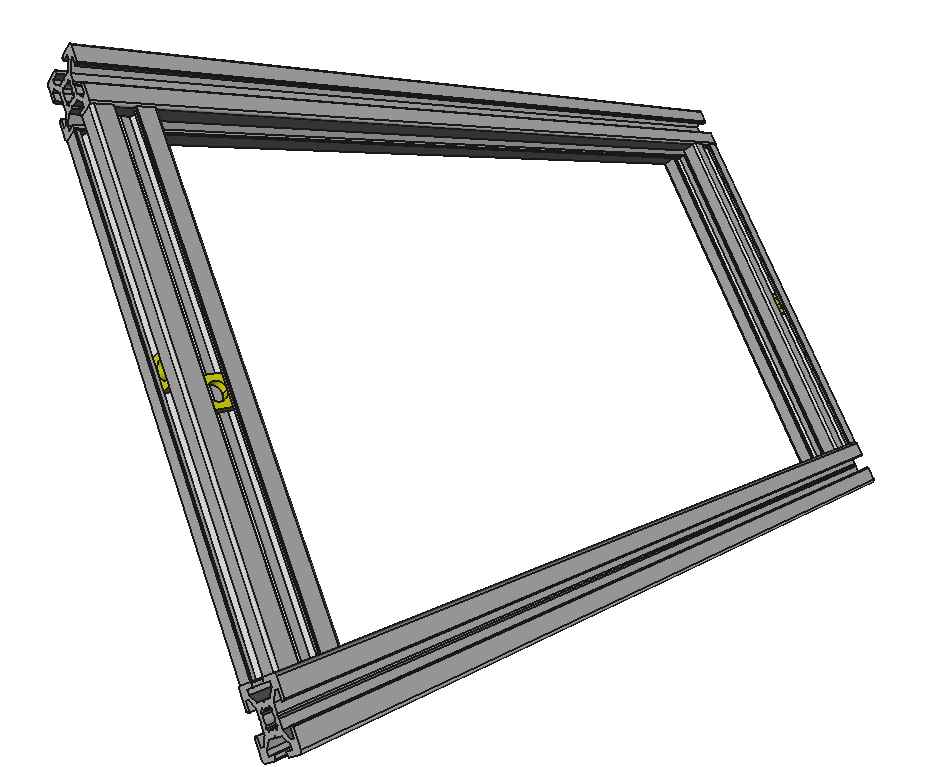
doc/src/src_boxassemblyguide1d/upper_frame/frame5.png
