case06/libresolarbox-v2_mobile/doc/src/src_boxassemblyguide1d/upright/corner5.png

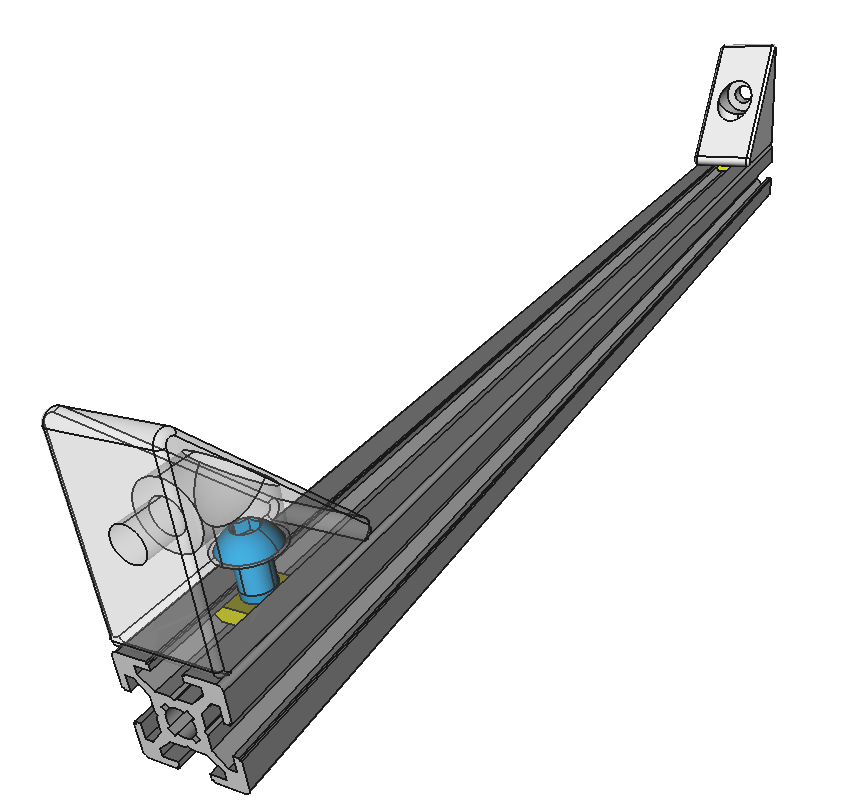
doc/src/src_boxassemblyguide1d/upright/corner5.png
