case06/libresolarbox-v2_mobile/doc/src/src_boxassemblyguide1d/upright/corner6.png

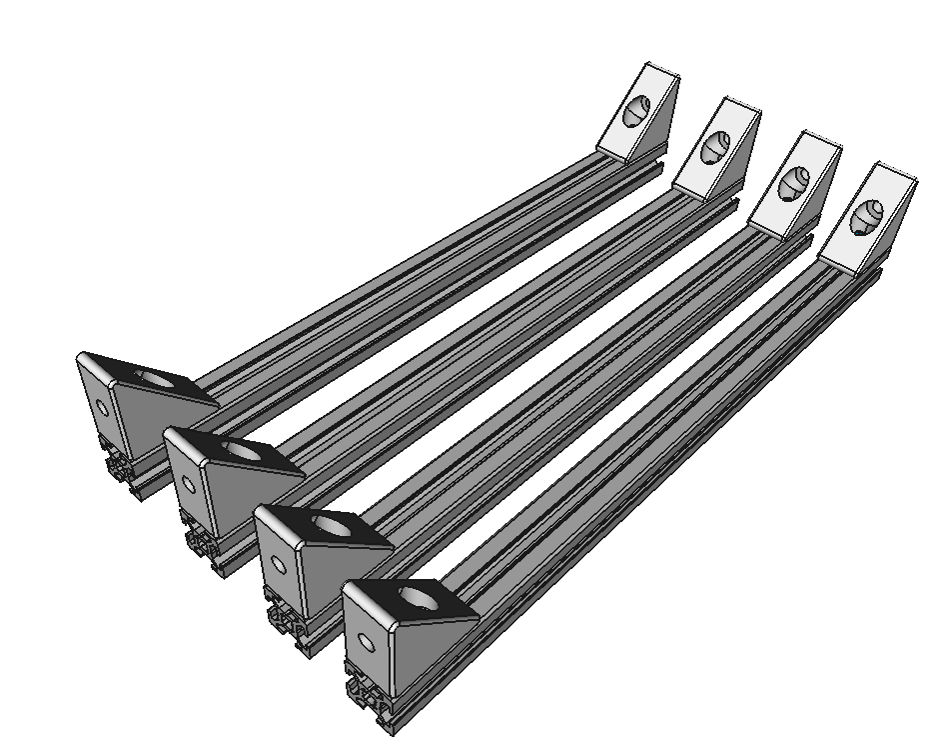
doc/src/src_boxassemblyguide1d/upright/corner6.png
